PHANNhatTien/Projet-Capteur-4e-INSATOULOUSE/Application bluetooth/Face_avant_application.jpg

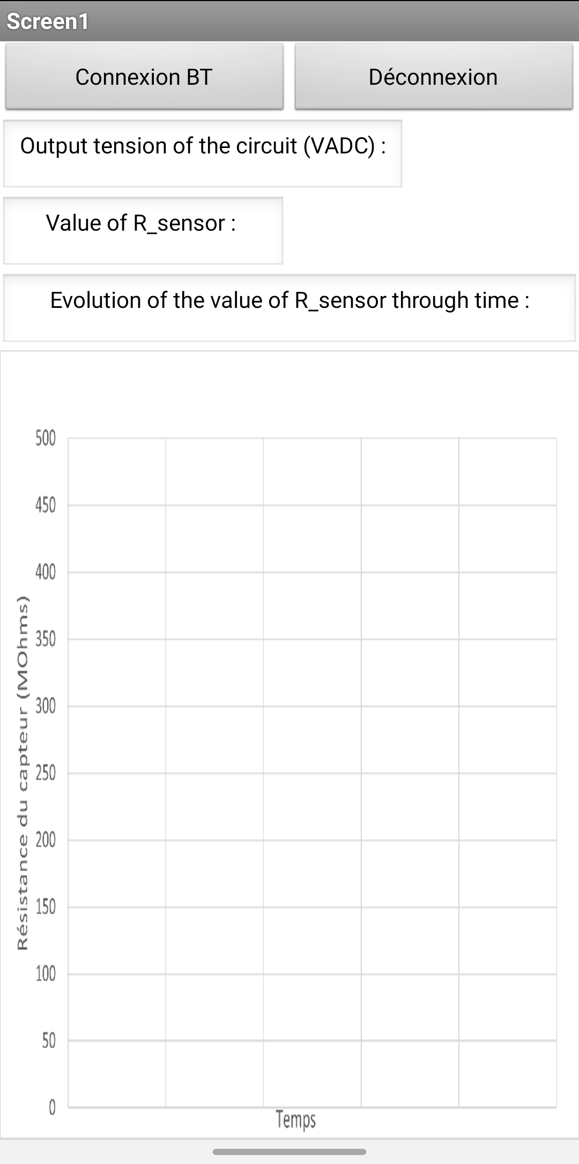
Application bluetooth/Face_avant_application.jpg
