PHANNhatTien/Projet-Capteur-4e-INSATOULOUSE/KiCAD-ProjetCapteur/Models/Bluetooth_HC-05/HC_05 Blue Tooth Module.JPG

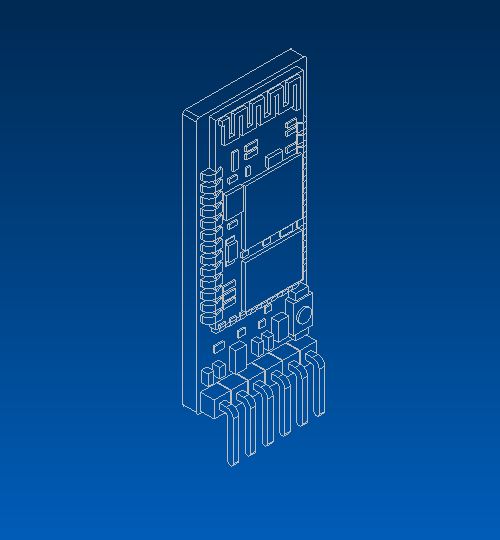
KiCAD-ProjetCapteur/Models/Bluetooth_HC-05/HC_05 Blue Tooth Module.JPG
