PHANNhatTien/Projet-Capteur-4e-INSATOULOUSE/KiCAD-ProjetCapteur/Models/display-oled-ssd1306-de-0-96-1.snapshot.6/OLED-128x64-0.96.png

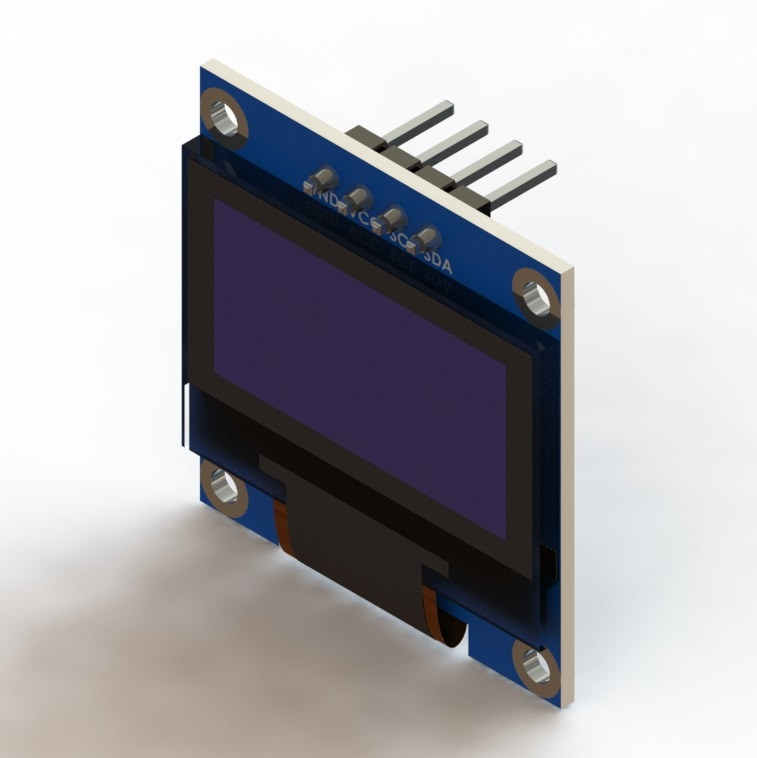
KiCAD-ProjetCapteur/Models/display-oled-ssd1306-de-0-96-1.snapshot.6/OLED-128x64-0.96.png
