PHANNhatTien/Projet-Capteur-4e-INSATOULOUSE/KiCAD-ProjetCapteur/Models/KY_040/image/left.png

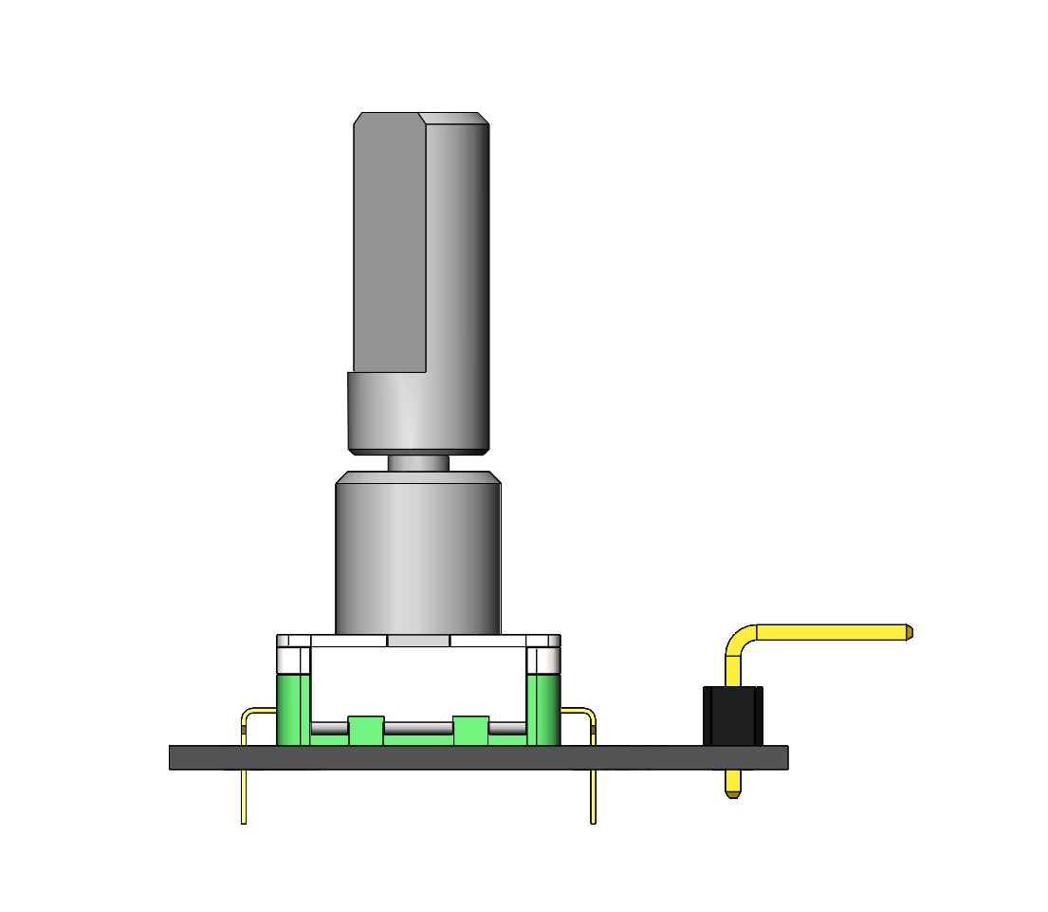
KiCAD-ProjetCapteur/Models/KY_040/image/left.png
