PHANNhatTien/Projet-Capteur-4e-INSATOULOUSE/KiCAD-ProjetCapteur/Models/KY_040/image/perspective 1 .png

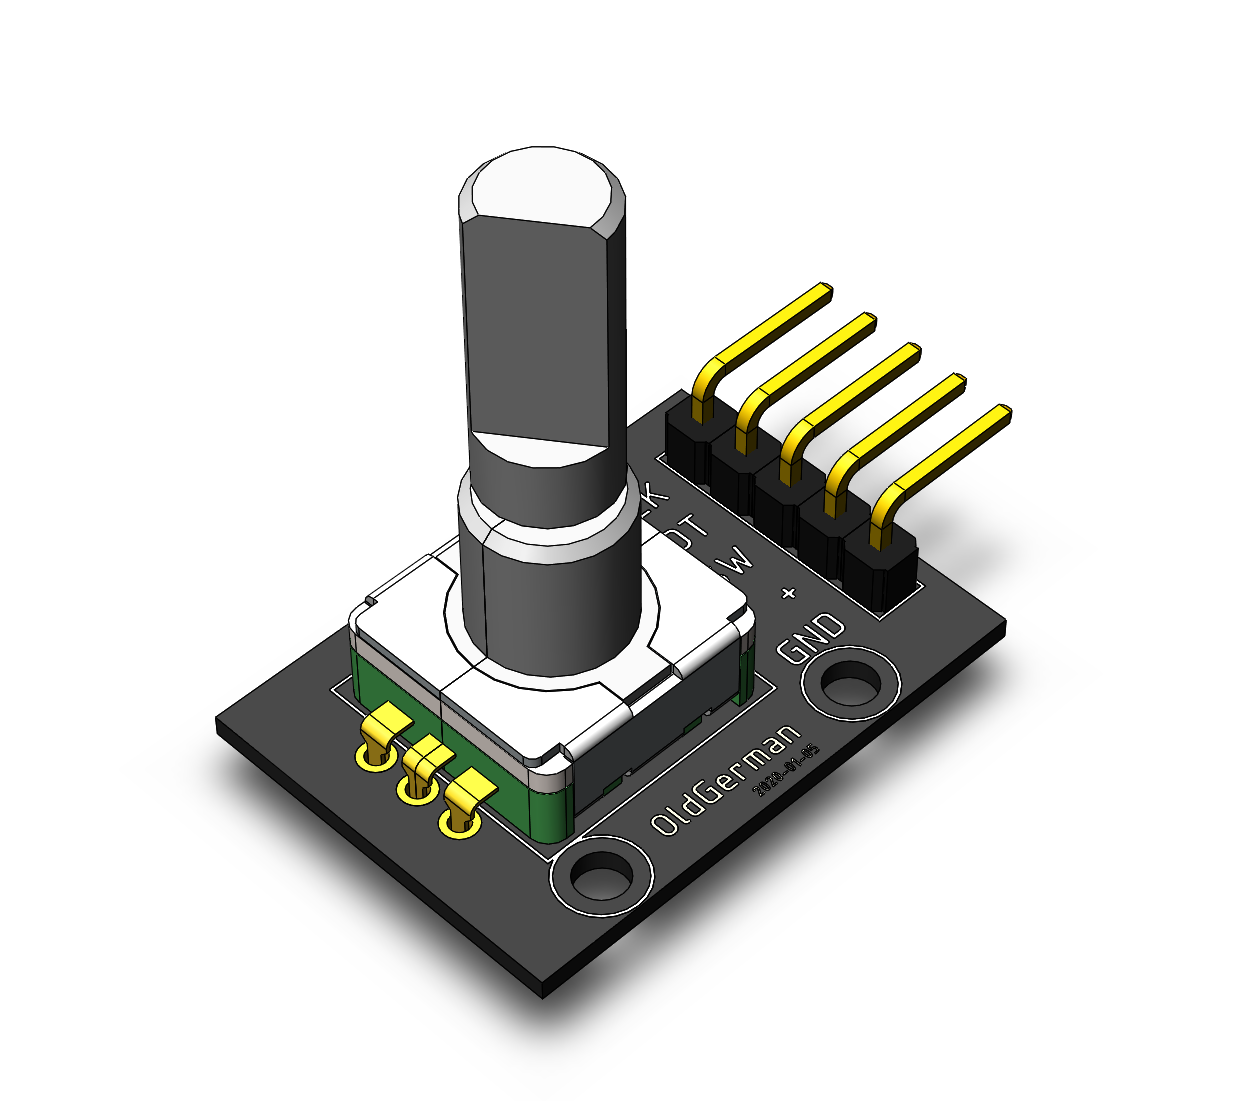
KiCAD-ProjetCapteur/Models/KY_040/image/perspective 1 .png
