PHANNhatTien/Projet-Capteur-4e-INSATOULOUSE/KiCAD-ProjetCapteur/Models/KY_040/image/top.png

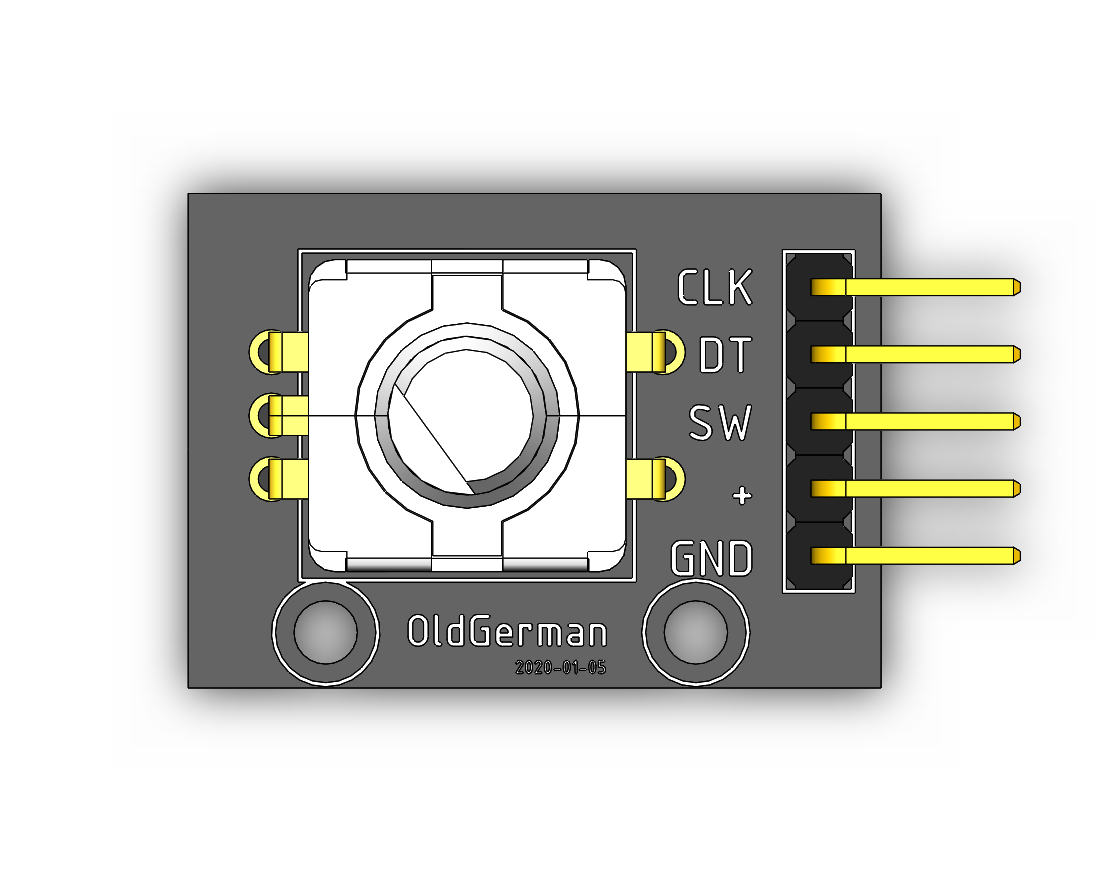
KiCAD-ProjetCapteur/Models/KY_040/image/top.png
