PHANNhatTien/Projet-Capteur-4e-INSATOULOUSE/KiCAD-ProjetCapteur/Models/pin_header/Pin_Header-Female-2.54mm_V3.png

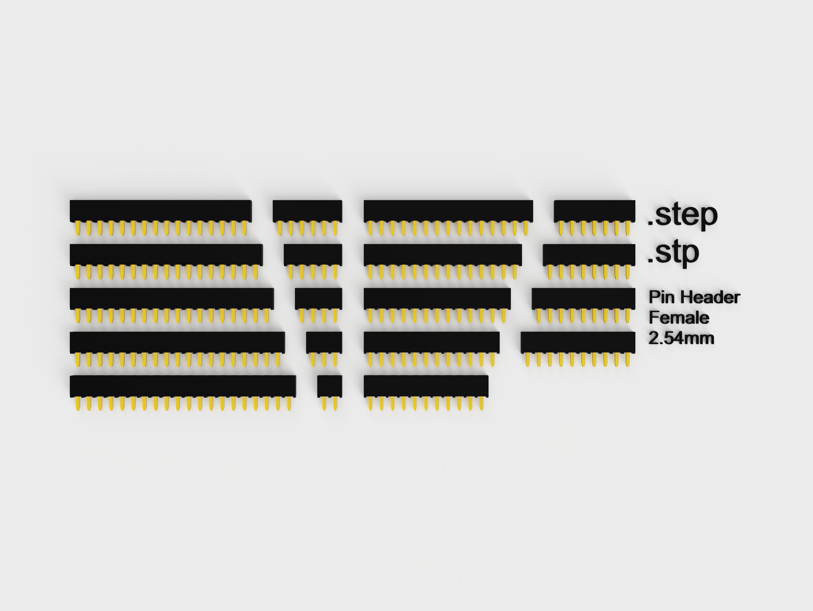
KiCAD-ProjetCapteur/Models/pin_header/Pin_Header-Female-2.54mm_V3.png
