PHANNhatTien/Projet-Capteur-4e-INSATOULOUSE/KiCAD-ProjetCapteur/Models/pin_header/18-Pin Header - Female - 2.54mm.step

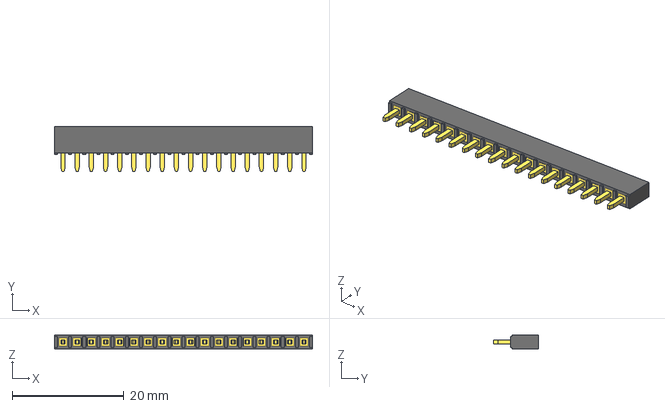
[picture p38: CAD file, 2023-04-13]
KiCAD-ProjetCapteur/Models/pin_header/18-Pin Header - Female - 2.54mm.step
46.2 x 8.00 x 2.50 mm
