PHANNhatTien/Projet-Capteur-4e-INSATOULOUSE/KiCAD-ProjetCapteur/Models/pin_header/13-Pin Header - Female - 2.54mm.step

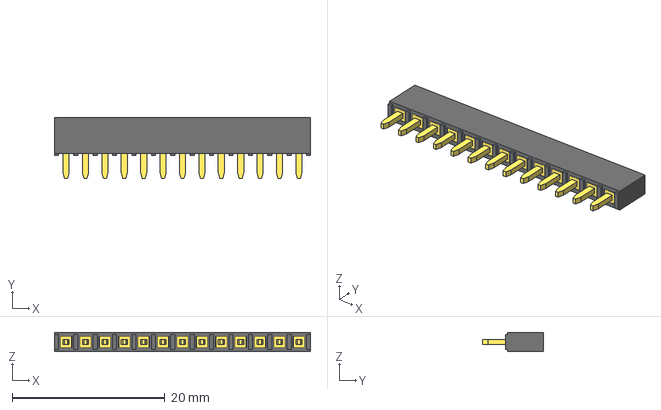
[picture p40: CAD file, 2023-04-13]
KiCAD-ProjetCapteur/Models/pin_header/13-Pin Header - Female - 2.54mm.step
33.5 x 8.00 x 2.50 mm
