PHANNhatTien/Projet-Capteur-4e-INSATOULOUSE/KiCAD-ProjetCapteur/Models/KY_040/image/Measured by hand.png

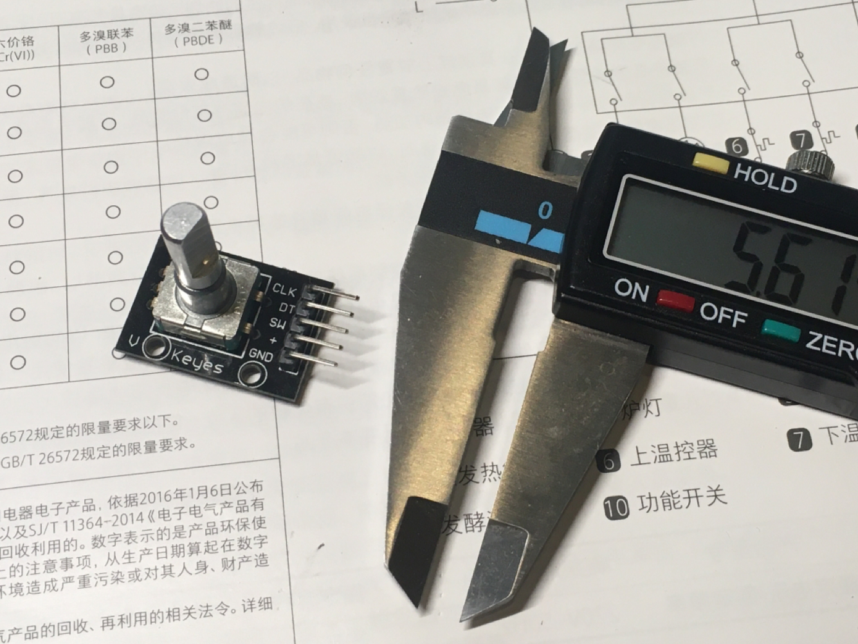
KiCAD-ProjetCapteur/Models/KY_040/image/Measured by hand.png
